S7uXN37/NineMensMorrisBoard/board/input.py

#!/usr/bin/env python
import RPi.GPIO as GPIO

# Import SPI library (for hardware SPI) and MCP3008 library.
import Adafruit_GPIO.SPI as SPI
import Adafruit_MCP3008

# Hardware SPI configuration:
SPI_PORT   = 0
SPI_DEVICE = 0
CS = [18,26,22]
mcp = Adafruit_MCP3008.MCP3008(spi=SPI.SpiDev(SPI_PORT, SPI_DEVICE))

lower_bound = 500
upper_bound = 547

GPIO.setmode(GPIO.BOARD)
for _cs in CS:
    GPIO.setup(_cs, GPIO.OUT, initial=GPIO.HIGH)

def read_mcp(cs):
    values = [0]*8
    for i in range(8):
        # The read_adc function will get the value of the specified channel (0-7).
        GPIO.output(cs, GPIO.LOW)
        v = mcp.read_adc(i)
        if v < lower_bound:
            values[i] = -1
        elif v > upper_bound:
            values[i] = 1
        else:
            values[i] = 0
        GPIO.output(cs, GPIO.HIGH)
    return values


def readBoard():
    i = read_mcp(CS[0])  # inner
    m = read_mcp(CS[1])  # middle
    o = read_mcp(CS[2])  # outer
    # map from polar coordinates (ring, pos in ring) to 1D array for AI
    board = [o[3], o[4], o[5],   m[3], m[4], m[5],   i[3], i[4], i[5],
             o[2], m[2], i[2],   i[6], m[6], o[6],
             i[1], i[0], i[7],   m[1], m[0], m[7],   o[1], o[0], o[7]]
    return board

def shutdown():
    GPIO.output(CS, GPIO.HIGH)
