S7uXN37/NineMensMorrisBoard/gpio-tests/magnet_test.py

import RPi.GPIO as GPIO
import time

pinA = 11
pinB = 13

GPIO.setmode(GPIO.BOARD)
GPIO.setup([pinA, pinB], GPIO.OUT, initial=GPIO.LOW)

def set(dir):
    if dir == 0:
        GPIO.output(pinA, GPIO.LOW)
        GPIO.output(pinB, GPIO.LOW)
    elif dir > 0:
        GPIO.output(pinA, GPIO.HIGH)
        GPIO.output(pinB, GPIO.LOW)
    else:
        GPIO.output(pinA, GPIO.LOW)
        GPIO.output(pinB, GPIO.HIGH)

try:
    i = 0
    while True:
        #dir = int(raw_input("Direction: "))
        dir = i%3 -1
        set(dir)
        print(dir)
        time.sleep(1)
        i+=1
except KeyboardInterrupt:
    GPIO.output([pinA, pinB], GPIO.LOW)
    GPIO.cleanup()
